YazawaKenichi/Murakumo/inventor/STL/MotorBracketv3.stl

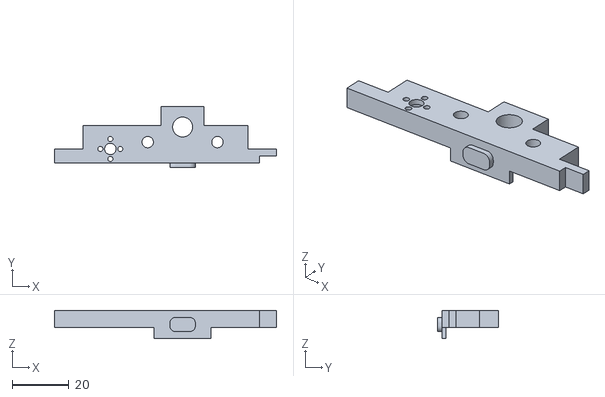
[picture p15: CAD file, 2022-08-05]
inventor/STL/MotorBracketv3.stl
78.0 x 21.6 x 10.0
