YazawaKenichi/Murakumo/inventor/STL/wheel_v8.stl

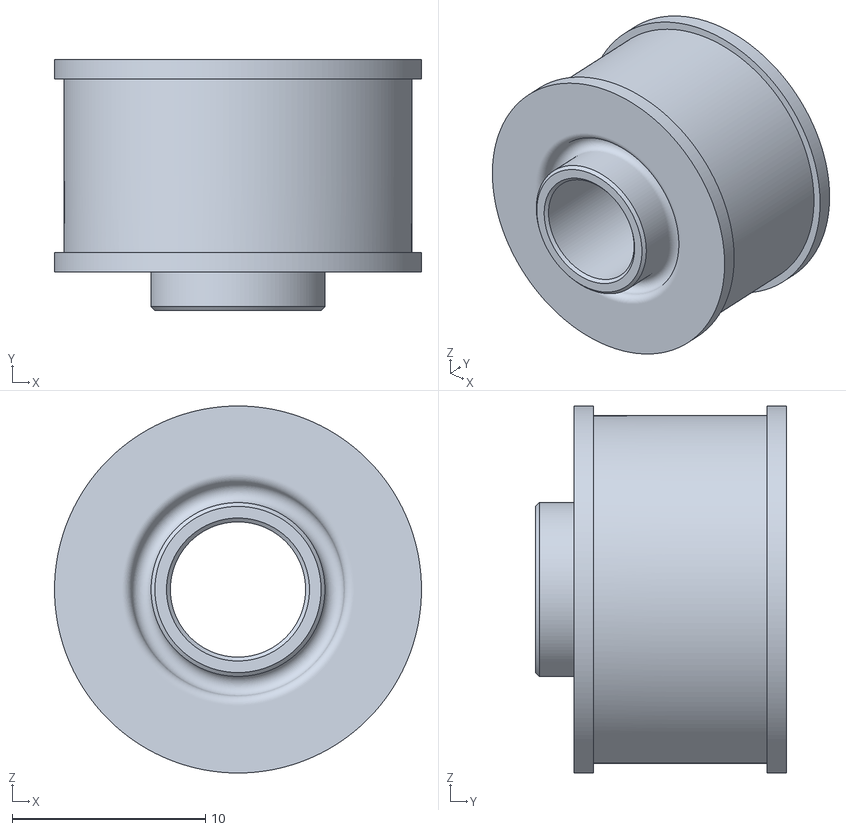
[picture p16: CAD file, 2022-08-05]
inventor/STL/wheel_v8.stl
19.0 x 13.0 x 19.0
