YazawaKenichi/Murakumo/inventor/STL/zig41.stl

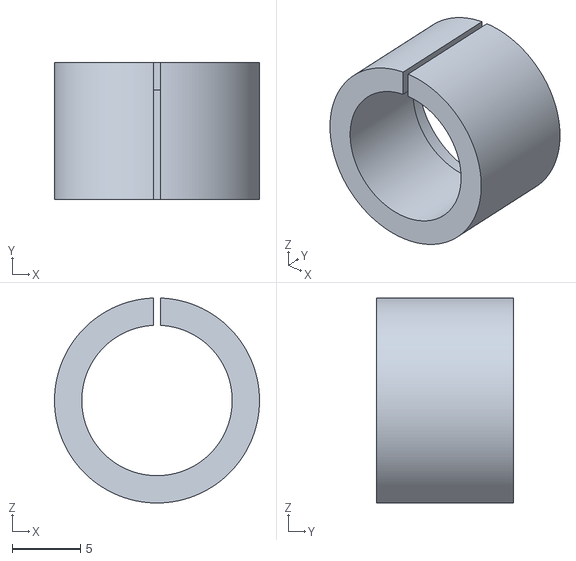
[picture p17: CAD file, 2022-03-09]
inventor/STL/zig41.stl
15.0 x 10.0 x 15.0
