YazawaKenichi/Murakumo/inventor/STL/wheelcap.stl

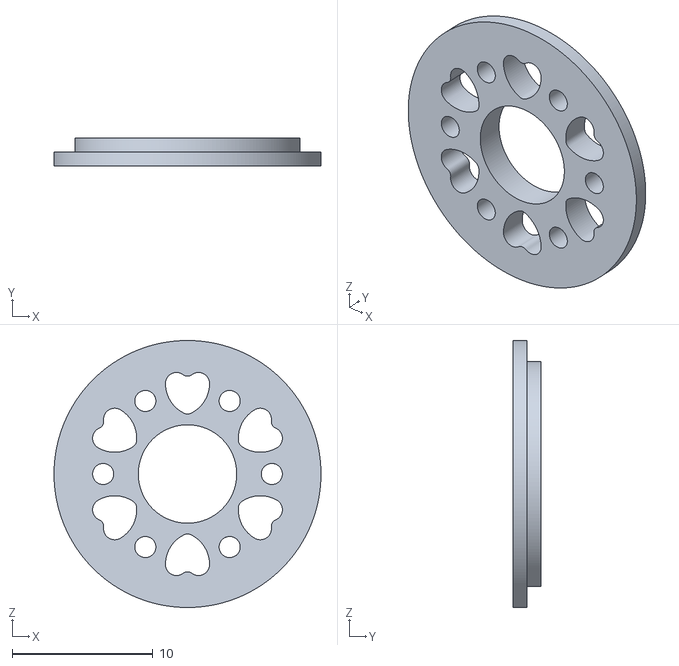
[picture p18: CAD file, 2022-03-09]
inventor/STL/wheelcap.stl
19.0 x 2.00 x 19.0
