YazawaKenichi/Murakumo/inventor/STL/zig64.stl

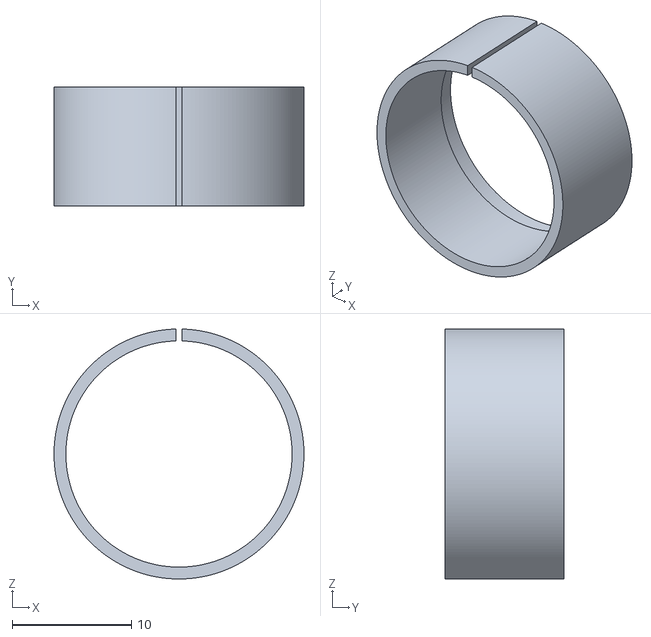
[picture p19: CAD file, 2022-03-09]
inventor/STL/zig64.stl
21.0 x 10.0 x 21.0
