YazawaKenichi/Murakumo/programs/murakumo_special/Core/Src/ICM20648.c

//ICM_20648.c Ver.1.3
#include "ICM20648.h"

#define USE_NCS 1
#define INIT_ZERO 1

//volatile int16_t xa, ya, za;
//volatile int16_t xg, yg, zg;

volatile Inertial inertial;
volatile Displacement displacement;
volatile Inertial inertial_offset;

Coordinate COORDINATE_ZERO;

uint8_t read_byte( uint8_t reg )
{
	uint8_t ret,val;

	ret = reg | 0x80;
#if USE_NCS
	CS_RESET;
#endif
	HAL_SPI_Transmit(&hspi2,&ret,1,100);
	HAL_SPI_Receive(&hspi2,&val,1,100);
#if USE_NCS
	CS_SET;
#endif

	return val;
}

void write_byte( uint8_t reg, uint8_t val )
{
	uint8_t ret;

	ret = reg & 0x7F;
#if USE_NCS
	CS_RESET;
#endif
	HAL_SPI_Transmit(&hspi2,&ret,1,100);
	HAL_SPI_Transmit(&hspi2,&val,1,100);
#if USE_NCS
	CS_SET;
#endif
}

uint8_t IMU_init(uint8_t* wai)
{
	CS_RESET;
	uint8_t who_am_i,ret;
	ret = 0;

	COORDINATE_ZERO.x = 0;
	COORDINATE_ZERO.y = 0;
	COORDINATE_ZERO.z = 0;

#if	INIT_ZERO
	inertial.accel = COORDINATE_ZERO;
	inertial.gyro = COORDINATE_ZERO;
	displacement.position = COORDINATE_ZERO;
	displacement.theta = COORDINATE_ZERO;
#endif

	/*
	xg = 0;
	yg = 0;
	zg = 0;
	xa = 0;
	ya = 0;
	za = 0;
	*/

	who_am_i = read_byte(0x00);
	*wai = who_am_i;
	if ( who_am_i == 0xE0 )
	{	// ICM-20648 is 0xE0
		ret = 1;
		write_byte(PWR_MGMT_1,0x01);	//PWR_MGMT_1
		HAL_Delay(100);
		write_byte(USER_CTRL,0x10);	//USER_CTRL
		write_byte(REG_BANK_SEL,0x20);	//USER_BANK2
		// shimotoriharuki
		//write_byte(0x01,0x06);	//range±2000dps DLPF disable	// range+-2000
		// igc8810
		write_byte(0x01,0x07);	//range±2000dps DLPF enable DLPFCFG = 0
		//write_byte(0x01,0x0F);	//range±2000dps DLPF enable DLPFCFG = 1
		//write_byte(0x01,0x17);	//range±2000dps DLPF enable DLPFCFG = 2
		//2:1 GYRO_FS_SEL[1:0] 00:±250	01:±500 10:±1000 11:±2000
		// igc8810
		write_byte(0x14,0x00);	//range±2g
		// shimotoriharuki
		//write_byte(0x14,0x06);	// range+-16
		//2:1 ACCEL_FS_SEL[1:0] 00:±2	01:±4 10:±8 11:±16
		write_byte(REG_BANK_SEL,0x00);	//USER_BANK0
		IMU_set_offset();
	}
#if USE_NCS
	CS_SET;
#endif
	return ret;
}

void IMU_fin()
{
#if !USE_NCS
	CS_SET;
#endif
}

void IMU_set_offset()
{
	IMU_read();
	inertial_offset = inertial;
}

void IMU_read()
{
	inertial.accel.x = ((int16_t)read_byte(ACCEL_XOUT_H) << 8) | ((int16_t)read_byte(ACCEL_XOUT_L));
	inertial.accel.y = ((int16_t)read_byte(ACCEL_YOUT_H) << 8) | ((int16_t)read_byte(ACCEL_YOUT_L));
	inertial.accel.z = ((int16_t)read_byte(ACCEL_ZOUT_H) << 8) | ((int16_t)read_byte(ACCEL_ZOUT_L));
	inertial.gyro.x = ((int16_t)read_byte(GYRO_XOUT_H) << 8) | ((int16_t)read_byte(GYRO_XOUT_L));
	inertial.gyro.y = ((int16_t)read_byte(GYRO_YOUT_H) << 8) | ((int16_t)read_byte(GYRO_YOUT_L));
	inertial.gyro.z = ((int16_t)read_byte(GYRO_ZOUT_H) << 8) | ((int16_t)read_byte(GYRO_ZOUT_L));
}

void Inertial_Integral(Displacement *a)
{
	IMU_read();
	a->position.x += inertial.accel.x;
	a->position.y += inertial.accel.y;
	a->position.z += inertial.accel.z;
	a->theta.x += inertial.gyro.x;
	a->theta.y += inertial.gyro.y;
	a->theta.z += inertial.gyro.z;
}

void Coordinate_Init(Coordinate *a)
{
	a->x = 0;
	a->y = 0;
	a->z = 0;
}
